JohnRobertoNau/e-book-reader/Images/placa-3d-cu-componente_1.png

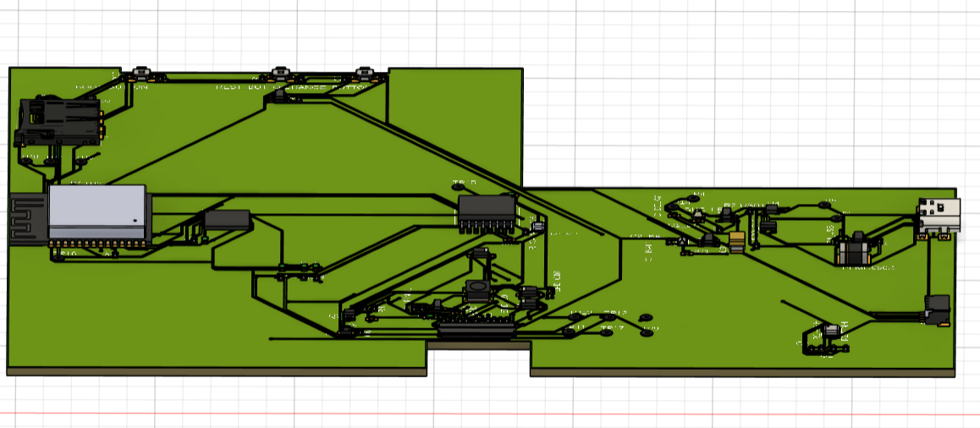
Images/placa-3d-cu-componente_1.png
